YJBeetle/NekoNoAshiFixture/Clip/Circuit/Kicad/Clip.kicad_sch

## KiCad design Clip/Circuit/Kicad/Clip.kicad_sch (2026-08-22)

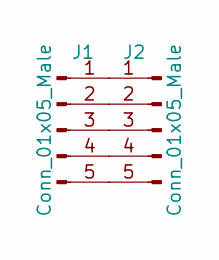
[picture p6: schematic Clip.kicad_sch]

Parts:
J1: Conn_01x05_Male; PinHeader_1x05_P2.54mm_Horizontal
J2: Conn_01x05_Male; moew_adapter

Connections:
unnamed: J1.1, J2.1
unnamed: J1.2, J2.2
unnamed: J1.3, J2.3
unnamed: J1.4, J2.4
unnamed: J1.5, J2.5
